teemune/sim-racing-instrument-panel/gear-display/LTspice/555_osc.asc

C1: cap; 100n
C2: cap; 10n
D1: diode
D2: diode
R1: res; 100
R2: res; 5k
R3: res; 1
R4: res; 1k
U1: NE555
V1: voltage; 5
Named nets: 0
.tran 0 10m 0
